alaminwiki/ESP32-S3-DevKitM-1_PCB_Design_in_Altium_Designer/Footprint & 3D Model/27_Ohm_Resistor Footprint/smd-resistor-0402-1005-0ohm-1.snapshot.3/image_2022-10-19_14-46-59.png

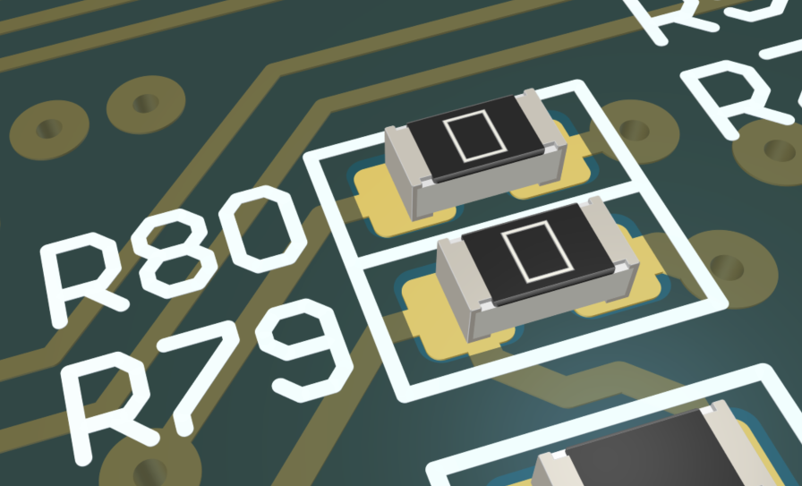
Footprint & 3D Model/27_Ohm_Resistor Footprint/smd-resistor-0402-1005-0ohm-1.snapshot.3/image_2022-10-19_14-46-59.png
