alaminwiki/ESP32-S3-DevKitM-1_PCB_Design_in_Altium_Designer/Footprint & 3D Model/27_Ohm_Resistor Footprint/smd-resistor-0402-1005-0ohm-1.snapshot.3/RESC1005X04L_-_0ohm_2022-Oct-19_12-45-31PM-000_CustomizedView14880564683.png

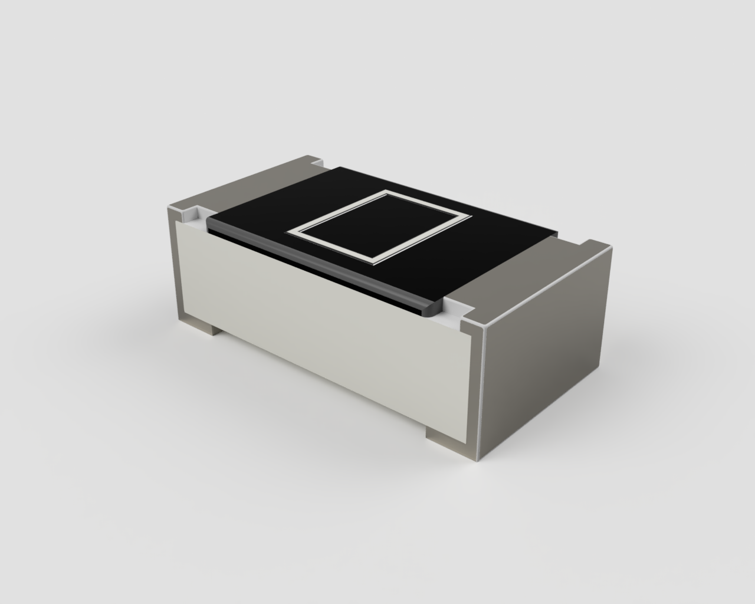
Footprint & 3D Model/27_Ohm_Resistor Footprint/smd-resistor-0402-1005-0ohm-1.snapshot.3/RESC1005X04L_-_0ohm_2022-Oct-19_12-45-31PM-000_CustomizedView14880564683.png
