alaminwiki/ESP32-S3-DevKitM-1_PCB_Design_in_Altium_Designer/Screenshot 2025-06-04 180434.png

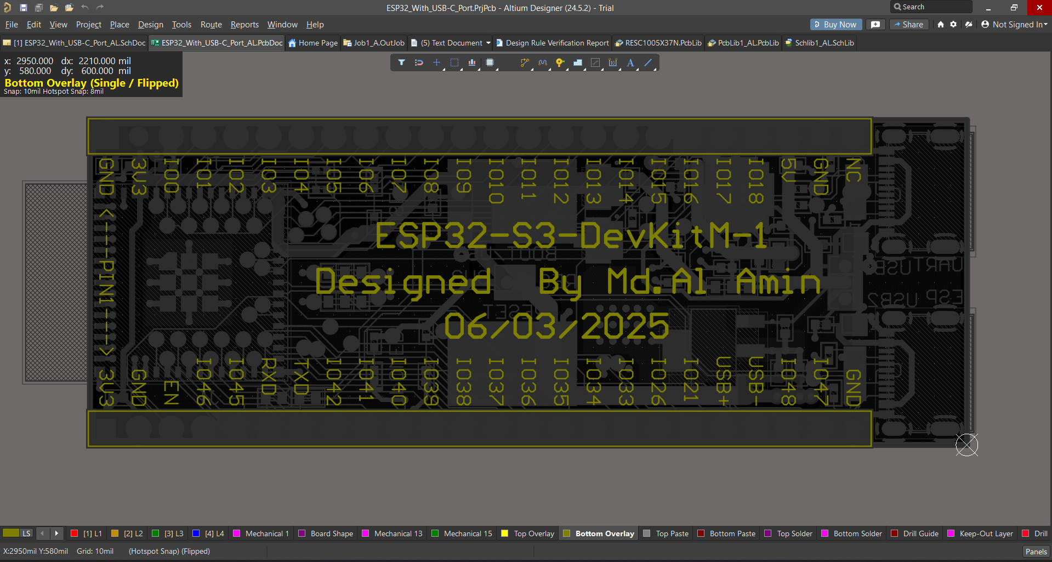
Screenshot 2025-06-04 180434.png
