alaminwiki/ESP32-S3-DevKitM-1_PCB_Design_in_Altium_Designer/Footprint & 3D Model/FTDI/FT231XQ_R_Ultra/AltiumDesigner/QFN20_FT231XQ_FTD.step

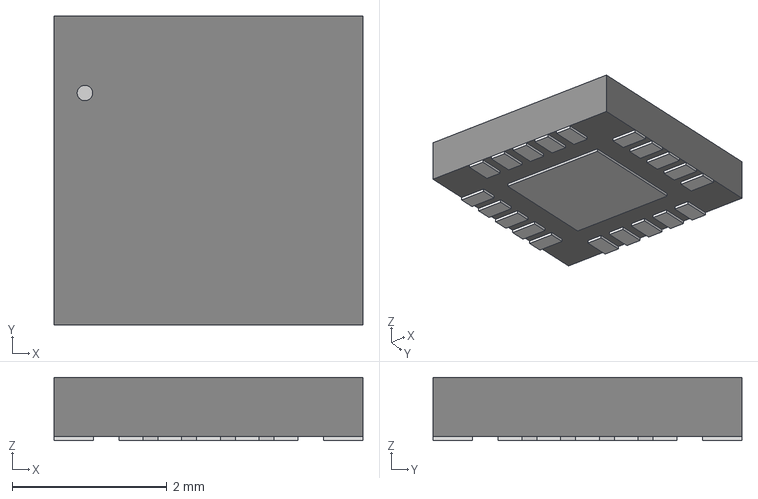
[picture p32: CAD file, 2025-06-04]
Footprint & 3D Model/FTDI/FT231XQ_R_Ultra/AltiumDesigner/QFN20_FT231XQ_FTD.step
3.99 x 3.99 x 0.815 mm
