alaminwiki/ESP32-S3-DevKitM-1_PCB_Design_in_Altium_Designer/Footprint & 3D Model/FTDI/FTDI_FT231XQ_R/FT231XQ-R.STEP

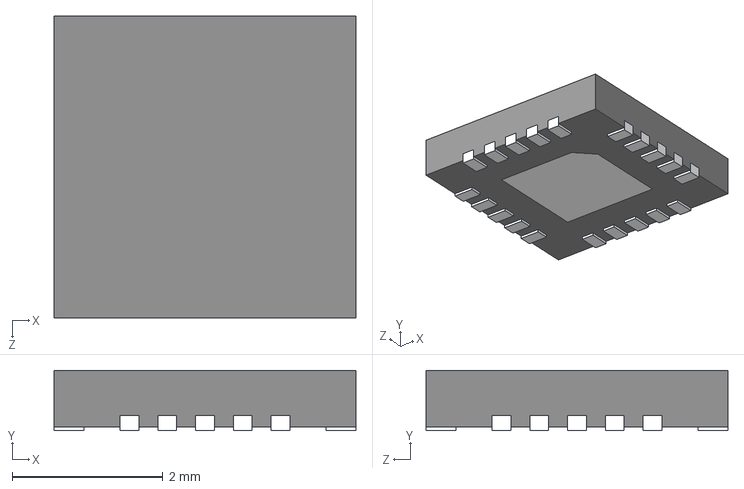
[picture p33: CAD file, 2025-06-04]
Footprint & 3D Model/FTDI/FTDI_FT231XQ_R/FT231XQ-R.STEP
4.00 x 0.8 x 4.00 mm
