alaminwiki/ESP32-S3-DevKitM-1_PCB_Design_in_Altium_Designer/Footprint & 3D Model/LED_RED_USER_LED/VLMS1500_GS08/AltiumDesigner/LED_00-GS08_VIS.step

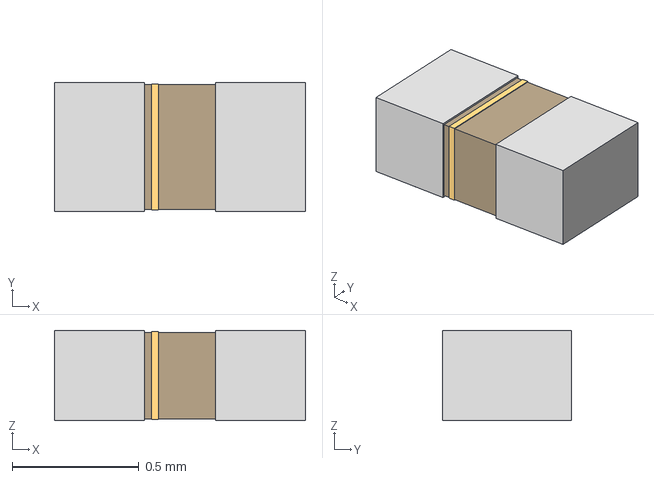
[picture p34: CAD file, 2025-06-04]
Footprint & 3D Model/LED_RED_USER_LED/VLMS1500_GS08/AltiumDesigner/LED_00-GS08_VIS.step
0.99 x 0.508 x 0.356 mm
