alaminwiki/ESP32-S3-DevKitM-1_PCB_Design_in_Altium_Designer/Footprint & 3D Model/LED_RED_USER_LED/VLMS1500_GS08/VLMx15xx_0402.stp

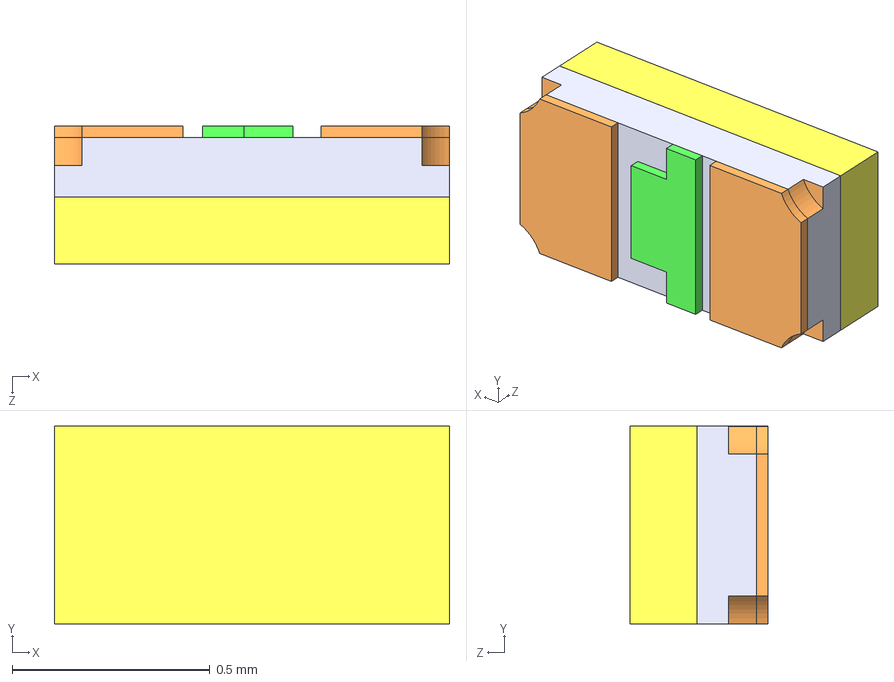
[picture p35: CAD file, 2025-06-04]
Footprint & 3D Model/LED_RED_USER_LED/VLMS1500_GS08/VLMx15xx_0402.stp
1.00 x 0.5 x 0.35 mm
C281-1
C281-2
C281-3
C281-4
C281-5
C281-6
C281-7
