alaminwiki/ESP32-S3-DevKitM-1_PCB_Design_in_Altium_Designer/Footprint & 3D Model/PTS645SH50SMTR92_LFS/PTS645SH50SMTR92 LFS.STEP

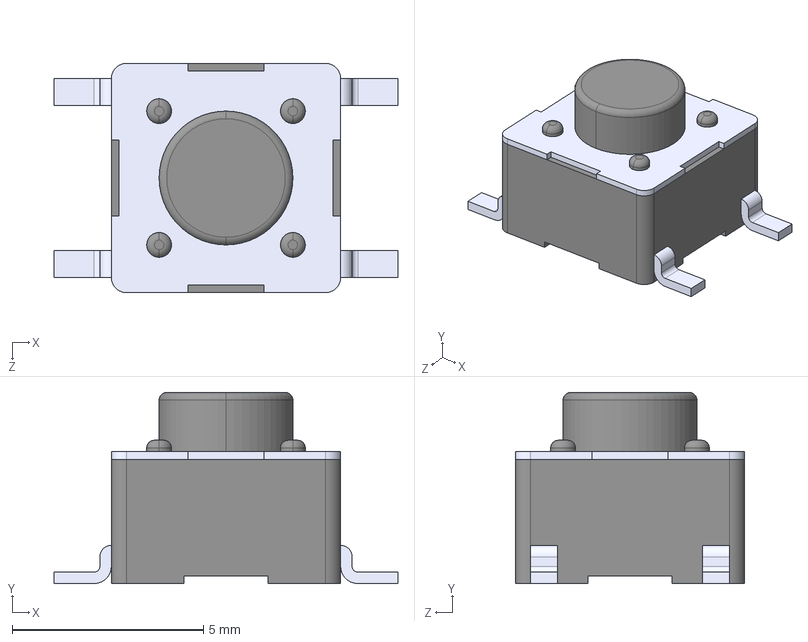
[picture p38: CAD file, 2025-06-04]
Footprint & 3D Model/PTS645SH50SMTR92_LFS/PTS645SH50SMTR92 LFS.STEP
9.00 x 5.00 x 6.00 mm
