alaminwiki/ESP32-S3-DevKitM-1_PCB_Design_in_Altium_Designer/Footprint & 3D Model/TL1963A_33DCYR/TL1963A-33DCYR.step

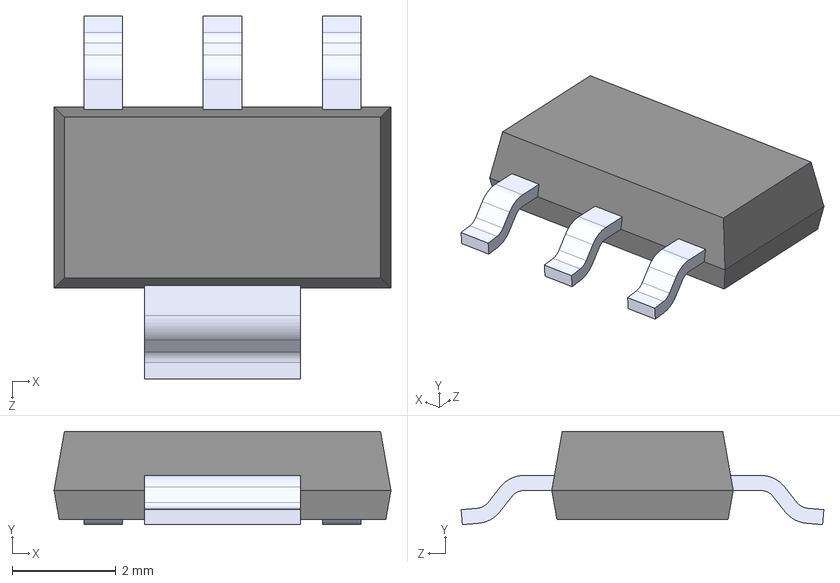
[picture p39: CAD file, 2025-06-04]
Footprint & 3D Model/TL1963A_33DCYR/TL1963A-33DCYR.step
6.50 x 1.80 x 7.00 mm
