alaminwiki/ESP32-S3-DevKitM-1_PCB_Design_in_Altium_Designer/Footprint & 3D Model/1K Resistor Snap/resistor-0402-1.snapshot.5/Resistor_0402_Ohm.step

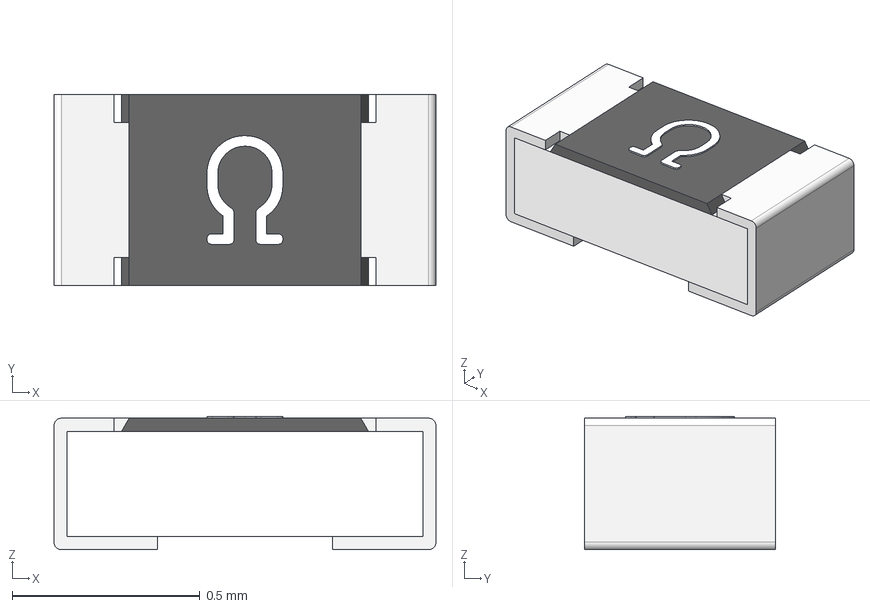
[picture p40: CAD file, 2025-06-04]
Footprint & 3D Model/1K Resistor Snap/resistor-0402-1.snapshot.5/Resistor_0402_Ohm.step
1.02 x 0.508 x 0.355 mm
Pin1Body
Pin2Body
CeramicBody
CoatingBody
TextBody
