alaminwiki/ESP32-S3-DevKitM-1_PCB_Design_in_Altium_Designer/Footprint & 3D Model/LED_USER_LED---RED/led-0402-0603-0805-1206-1.snapshot.1/LED0402.STEP

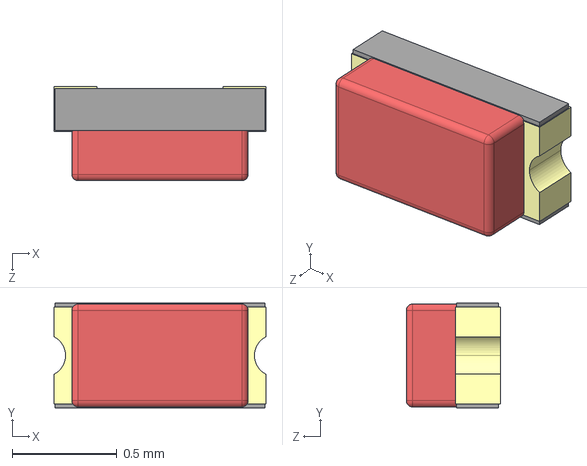
[picture p41: CAD file, 2025-06-04]
Footprint & 3D Model/LED_USER_LED---RED/led-0402-0603-0805-1206-1.snapshot.1/LED0402.STEP
1.01 x 0.5 x 0.45 mm
