alaminwiki/ESP32-S3-DevKitM-1_PCB_Design_in_Altium_Designer/Footprint & 3D Model/1K Resistor Snap/resistor-0402-1.snapshot.5/Resistor_0402.step

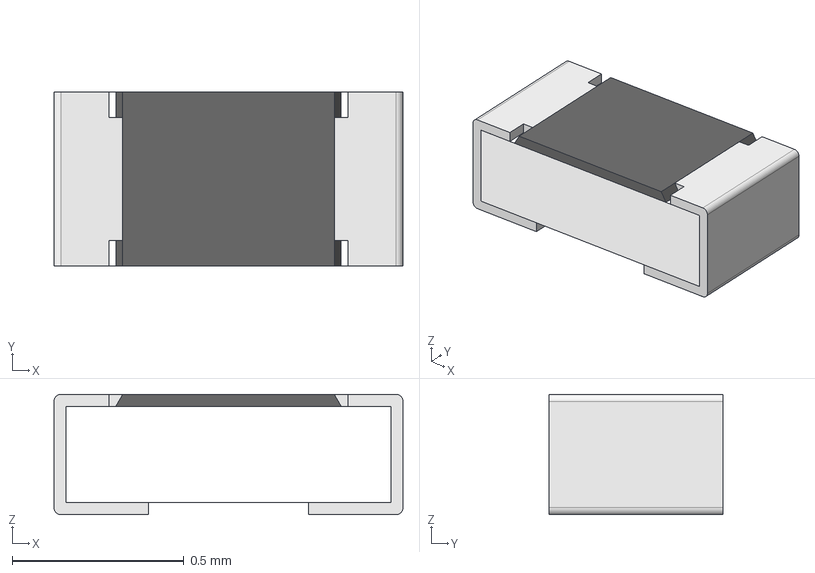
[picture p42: CAD file, 2025-06-04]
Footprint & 3D Model/1K Resistor Snap/resistor-0402-1.snapshot.5/Resistor_0402.step
1.02 x 0.508 x 0.35 mm
Pin1
Pin2
CeramicBody
Coating
