alaminwiki/ESP32-S3-DevKitM-1_PCB_Design_in_Altium_Designer/Footprint & 3D Model/LED_USER_LED---RED/led-0402-0603-0805-1206-1.snapshot.1/LED0805.STEP

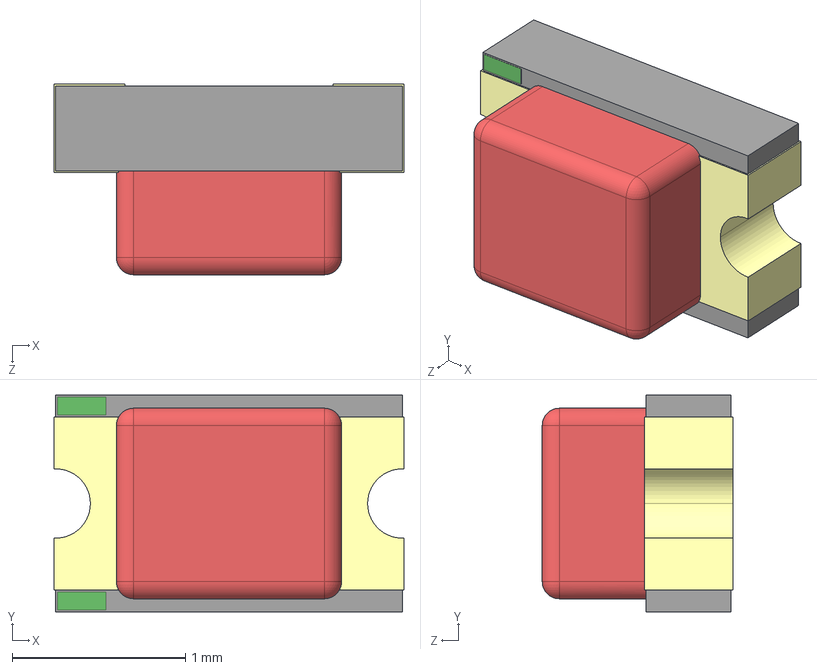
[picture p44: CAD file, 2025-06-04]
Footprint & 3D Model/LED_USER_LED---RED/led-0402-0603-0805-1206-1.snapshot.1/LED0805.STEP
2.02 x 1.25 x 1.10 mm
