alaminwiki/ESP32-S3-DevKitM-1_PCB_Design_in_Altium_Designer/Footprint & 3D Model/1K Resistor Snap/resistor-0402-1.snapshot.5/Resistor_0402_Solder.step

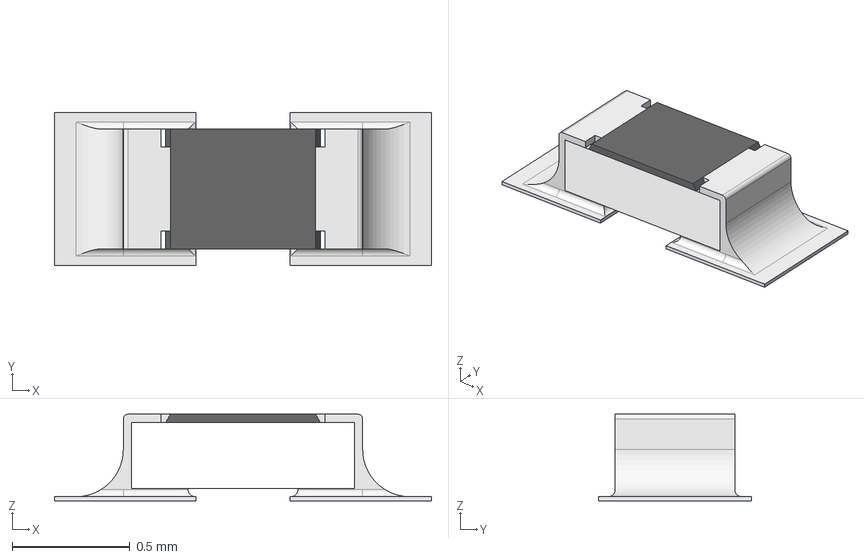
[picture p45: CAD file, 2025-06-04]
Footprint & 3D Model/1K Resistor Snap/resistor-0402-1.snapshot.5/Resistor_0402_Solder.step
1.60 x 0.65 x 0.367 mm
Pin1
Pin2
CeramicBody
Coating
