alaminwiki/ESP32-S3-DevKitM-1_PCB_Design_in_Altium_Designer/Footprint & 3D Model/LED_USER_LED---RED/led-0402-0603-0805-1206-1.snapshot.1/LED0603.STEP

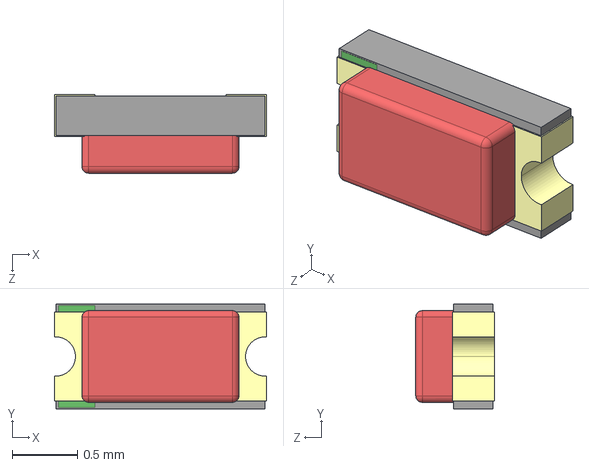
[picture p46: CAD file, 2025-06-04]
Footprint & 3D Model/LED_USER_LED---RED/led-0402-0603-0805-1206-1.snapshot.1/LED0603.STEP
1.62 x 0.8 x 0.6 mm
