alaminwiki/ESP32-S3-DevKitM-1_PCB_Design_in_Altium_Designer/Footprint & 3D Model/LED_USER_LED---RED/chipled-0402-smd-1.snapshot.3/ChipLedLens.stp

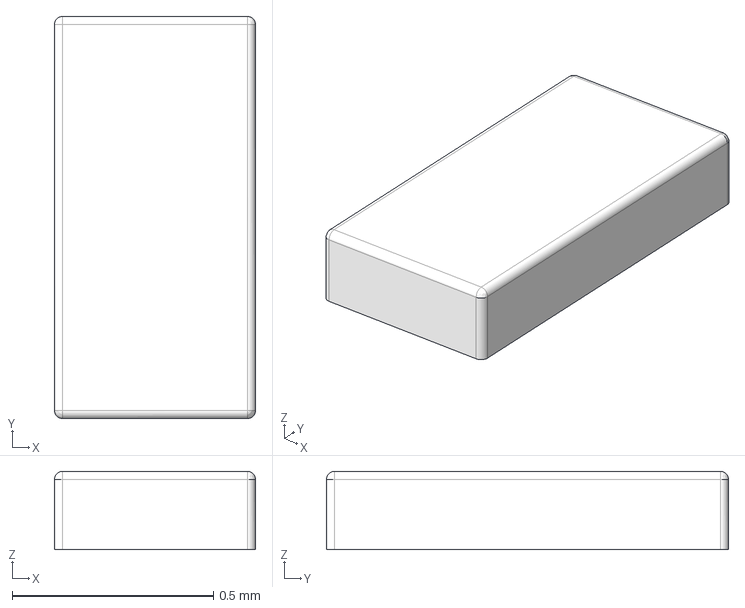
[picture p47: CAD file, 2025-06-04]
Footprint & 3D Model/LED_USER_LED---RED/chipled-0402-smd-1.snapshot.3/ChipLedLens.stp
0.5 x 1.00 x 0.195 mm
